Prathviraj-mv/CHIMAERA---Open-source-6-DOF-Robotic-arm/IMAGES/IMG_20250628_210149.jpg

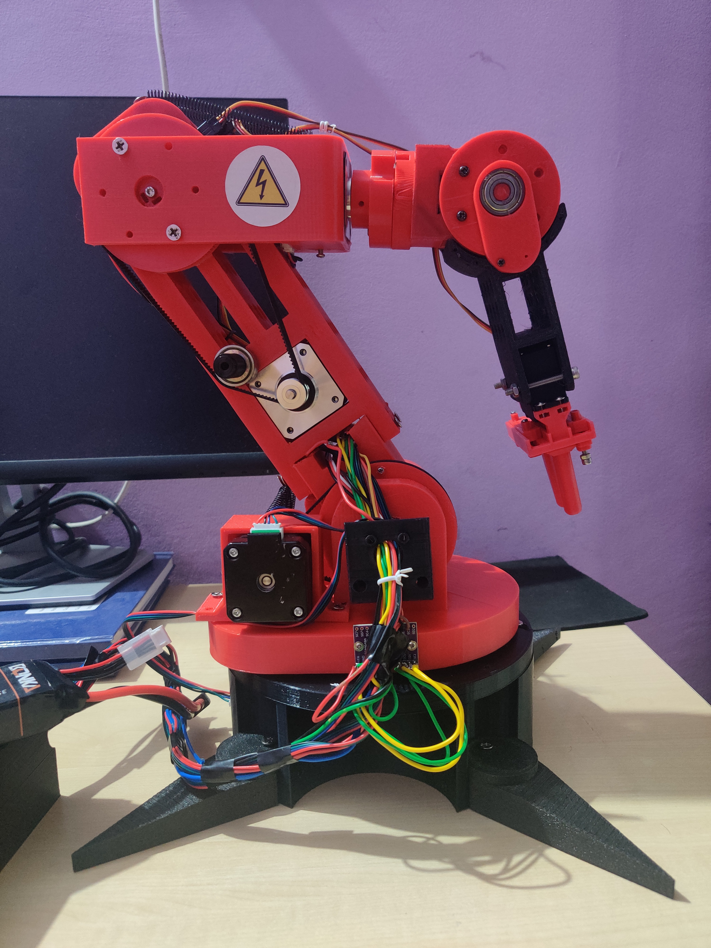
IMAGES/IMG_20250628_210149.jpg
